ubilab-ws21/puzzle-3/designs/3D_Modeling/microusb_5pin/1-1.png

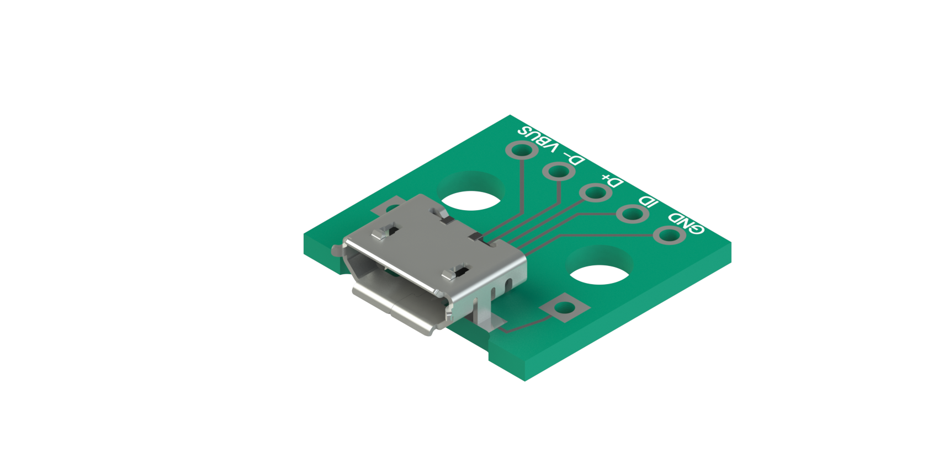
designs/3D_Modeling/microusb_5pin/1-1.png
