ubilab-ws21/puzzle-3/designs/3D_Manufactoring/leftPlate.dxf

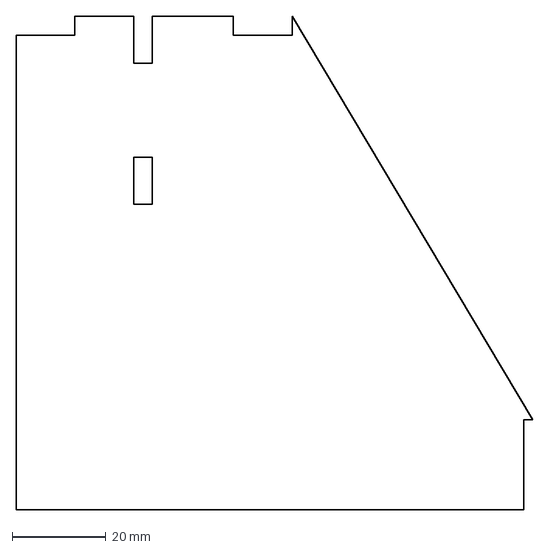
[picture p18: CAD file, 2022-01-20]
designs/3D_Manufactoring/leftPlate.dxf
110.0 x 105.0 mm
