ubilab-ws21/puzzle-3/designs/3D_Manufactoring/groundPlate.stl

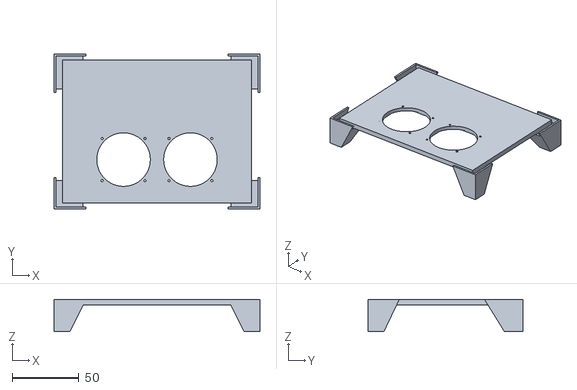
[picture p19: CAD file, 2022-01-20]
designs/3D_Manufactoring/groundPlate.stl
154.0 x 116.0 x 24.0
