ubilab-ws21/puzzle-3/designs/3D_Manufactoring/DisplayCircuitMount.stl

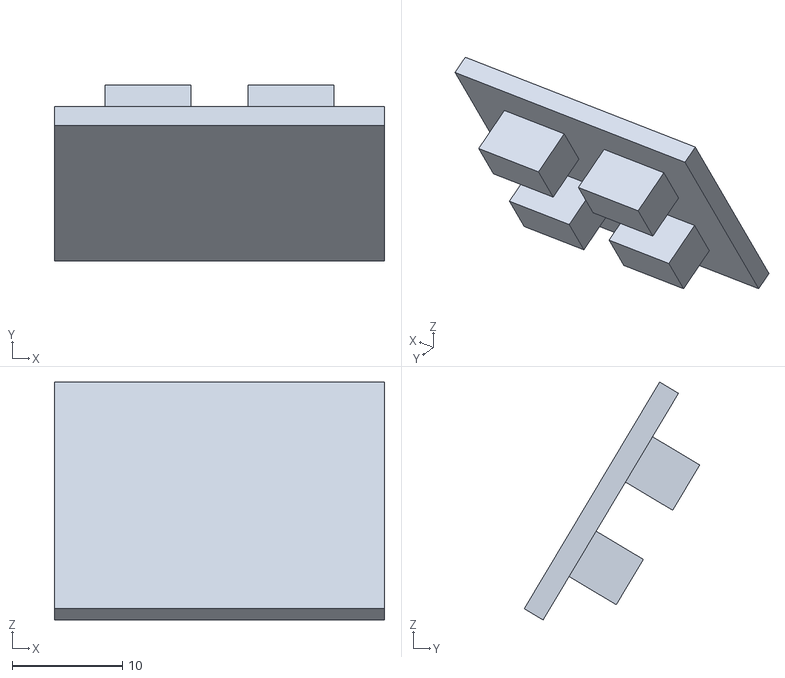
[picture p20: CAD file, 2022-01-20]
designs/3D_Manufactoring/DisplayCircuitMount.stl
30.0 x 16.0 x 21.6
