ubilab-ws21/puzzle-3/designs/3D_Manufactoring/antennaSupport.dxf

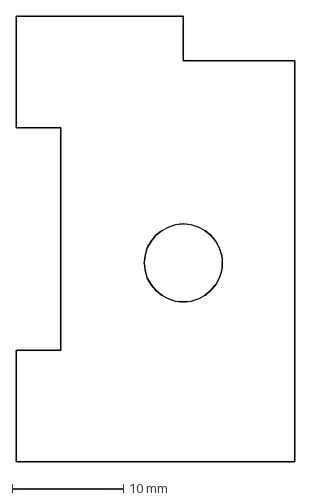
[picture p21: CAD file, 2022-01-20]
designs/3D_Manufactoring/antennaSupport.dxf
25.0 x 40.0 mm
