ubilab-ws21/puzzle-3/designs/3D_Manufactoring/rightPlate.dxf

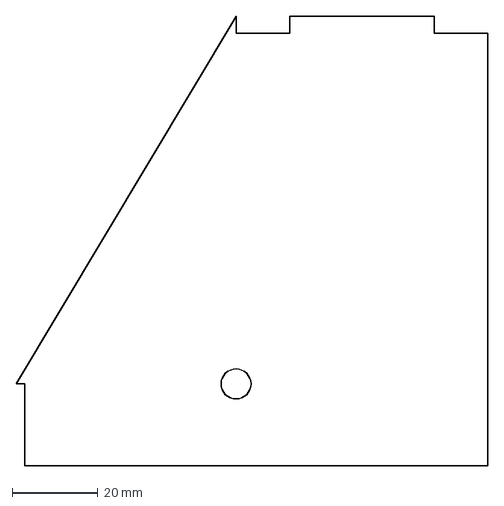
[picture p22: CAD file, 2022-01-20]
designs/3D_Manufactoring/rightPlate.dxf
110.0 x 105.0 mm
