ubilab-ws21/puzzle-3/Code/puzzle_display_control/include/encoder_handle.h

#ifndef ENCODER_HANDLE_H
#define ENCODER_HANDLE_H

#define NUM_ENCODERS_DEFINED 3

void init_encoder(void);
int check_game_encoders(void);
bool check_vol_encoder(int* new_volume);
unsigned int check_ant_encoder();

int encoder_get_value(int encoder_num);
void encoder_set_value(int encoder_num, int value);

#endif
